laneboysrc/rc-brake-lights/firmware/drive_mode.c

/******************************************************************************

    Simulates the state machine in the ESC and updates the variable drive_mode
    accordingly.

    +/-10: forward = 0, reverse = 0
    >+10: forward = 1, brake_armed = 1
    <-10:
      if brake_armed: brake = 1
      if not brake_armed: reverse = 1, brake = 0
    2 seconds in Neutral: brake_armed = 0
    Brake -> Neutral: brake = 0, brake_armed = 0
    Reverse -> Neutral: brake = 1 for 2 seconds

******************************************************************************/
#include <stdint.h>

#include "globals.h"


#define AUTO_BRAKE_COUNTER_VALUE_FORWARD_MIN  (500 / __SYSTICK_IN_MS)
#define AUTO_BRAKE_COUNTER_VALUE_FORWARD_MAX  (2500 / __SYSTICK_IN_MS)
#define AUTO_BRAKE_COUNTER_VALUE_REVERSE_MIN  (500 / __SYSTICK_IN_MS)
#define AUTO_BRAKE_COUNTER_VALUE_REVERSE_MAX  (2500 / __SYSTICK_IN_MS)
#define AUTO_REVERSE_COUNTER_VALUE_MIN  (800 / __SYSTICK_IN_MS)
#define AUTO_REVERSE_COUNTER_VALUE_MAX  (2000 / __SYSTICK_IN_MS)
#define BRAKE_DISARM_COUNTER_VALUE  (1000 / __SYSTICK_IN_MS)

// #define AUTO_BRAKE_LIGHTS_FORWARD_ENABLED true
// #define AUTO_BRAKE_LIGHTS_REVERSE_ENABLED true

#define CENTRE_THRESHOLD_LOW 8
#define CENTRE_THRESHOLD_HIGH 12


static uint16_t throttle_threshold = CENTRE_THRESHOLD_HIGH;
static uint16_t brake_disarm_counter;
static uint16_t auto_brake_counter;
static uint16_t auto_reverse_counter;

static struct {
    unsigned int brake_disarm : 1;
    unsigned int auto_brake : 1;
    unsigned int auto_reverse : 1;
    unsigned int brake_armed : 1;
} drive_mode;

ESC_MODE_T esc_mode;


// ****************************************************************************
static void throttle_neutral(void)
{
    throttle_threshold = CENTRE_THRESHOLD_HIGH;
    if (global_flags.forward) {
        global_flags.forward = false;

        // Handle ESC where reverse can be engaged after a certain time in
        // neutral
        if (esc_mode == ESC_FORWARD_BRAKE_REVERSE_TIMEOUT) {
            drive_mode.brake_disarm = true;
            brake_disarm_counter = BRAKE_DISARM_COUNTER_VALUE;
        }

        // if (AUTO_BRAKE_LIGHTS_FORWARD_ENABLED) {
            global_flags.braking = true;
            // The time the brake lights stay on after going back to neutral
            // is random
            drive_mode.auto_brake = true;
            auto_brake_counter = random_min_max(
                AUTO_BRAKE_COUNTER_VALUE_FORWARD_MIN,
                AUTO_BRAKE_COUNTER_VALUE_FORWARD_MAX);
        // }
    }
    else if (global_flags.reversing) {
        if (!drive_mode.auto_reverse) {
            drive_mode.auto_reverse = true;
            auto_reverse_counter = random_min_max(
                AUTO_REVERSE_COUNTER_VALUE_MIN,
                AUTO_REVERSE_COUNTER_VALUE_MAX);

            // if (AUTO_BRAKE_LIGHTS_REVERSE_ENABLED) {
                global_flags.braking = true;
                drive_mode.auto_brake = true;
                auto_brake_counter = random_min_max(
                    AUTO_BRAKE_COUNTER_VALUE_REVERSE_MIN,
                    AUTO_BRAKE_COUNTER_VALUE_REVERSE_MAX);
            // }
        }
    }
    else if (global_flags.braking) {
        if (!drive_mode.auto_brake) {
            drive_mode.brake_armed = false;
            global_flags.braking = false;
        }
    }
}


// ****************************************************************************
static void throttle_brake_or_reverse(void)
{
    if (esc_mode == ESC_FORWARD_BRAKE  ||  drive_mode.brake_armed) {
        global_flags.braking = true;
        global_flags.forward = false;
        global_flags.reversing = false;
    }
    else {
        global_flags.reversing = true;
        global_flags.braking = false;
        global_flags.forward = false;
        drive_mode.auto_reverse = false;
    }
}


// ****************************************************************************
static void throttle_not_neutral(void)
{
    throttle_threshold = CENTRE_THRESHOLD_LOW;
    drive_mode.auto_brake = false;
    drive_mode.brake_disarm = false;

    if (channel[TH].normalized < 0) {
        throttle_brake_or_reverse();
    }
    else {
        global_flags.forward = true;
        global_flags.reversing = false;
        global_flags.braking = false;
        if (esc_mode != ESC_FORWARD_REVERSE) {
           drive_mode.brake_armed = true;
        }
    }
}


// ****************************************************************************
void process_drive_mode(void)
{
    if (global_flags.systick) {
        if (drive_mode.brake_disarm) {
            if (--brake_disarm_counter == 0) {
                drive_mode.brake_disarm = false;
                drive_mode.brake_armed = false;
            }
        }

        if (drive_mode.auto_brake) {
            if (--auto_brake_counter == 0) {
                drive_mode.auto_brake = false;
                global_flags.braking = false;
            }
        }

        if (drive_mode.auto_reverse) {
            if (--auto_reverse_counter == 0) {
                drive_mode.auto_reverse = false;
                global_flags.reversing = false;
            }
        }
    }

    if (global_flags.new_channel_data) {
        if (channel[TH].absolute < throttle_threshold) {
            // We are in neutral
            throttle_neutral();
        }
        else {
            throttle_not_neutral();
        }
    }
}
